ChrisChrisLoLo/pusheenz40/photos/PXL_20240128_191046546.jpg

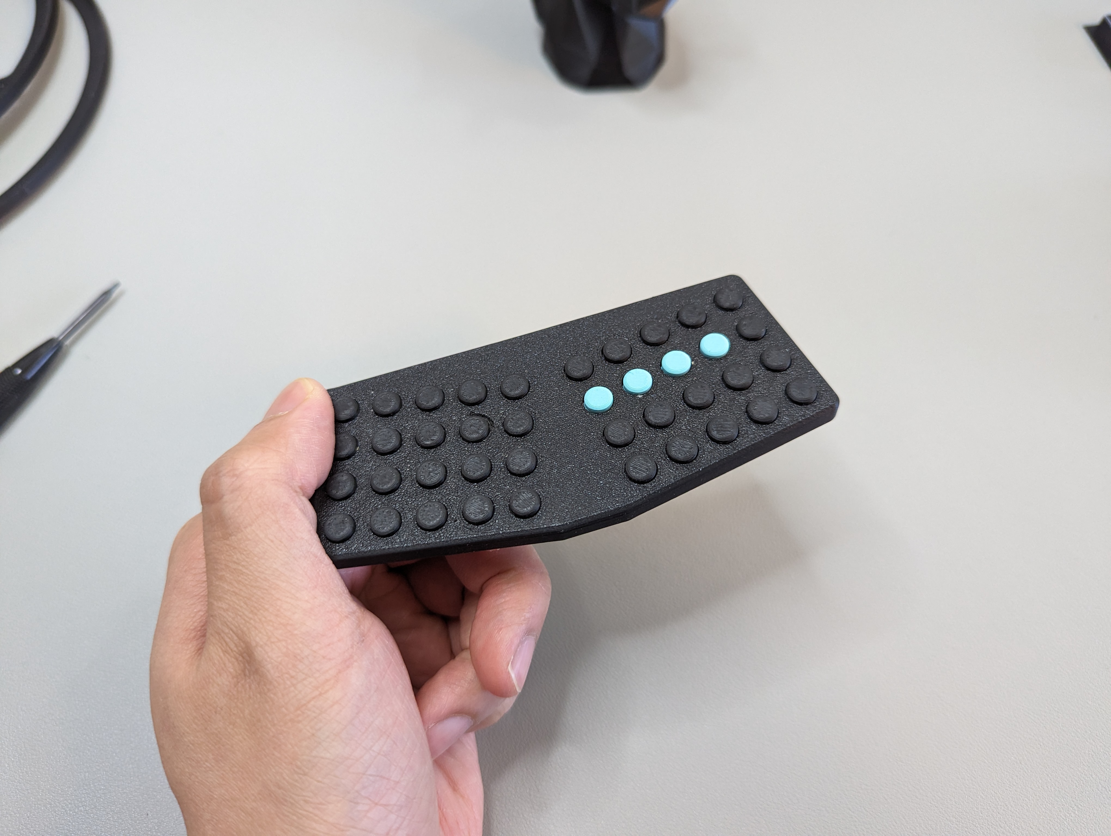
photos/PXL_20240128_191046546.jpg
